Basionie/DSP-Guitar-MultiFX/Mechanical/DSP_3D_Design/Geekcreit 1.3 Inch 4Pin.step.SLDPRT

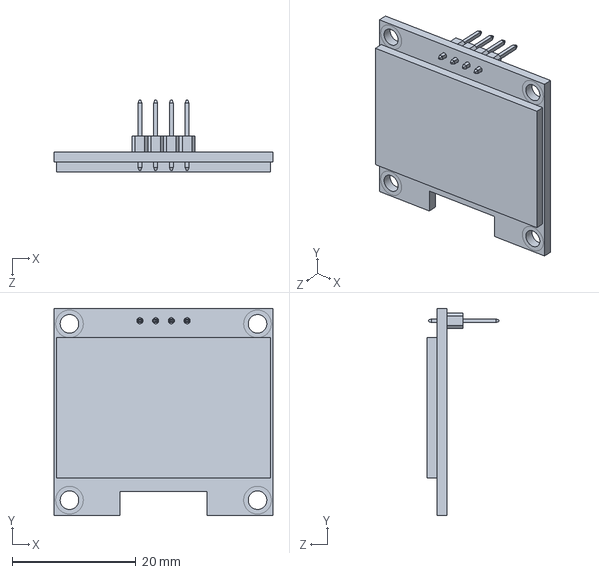
[picture p17: CAD file, 2026-07-20]
Mechanical/DSP_3D_Design/Geekcreit 1.3 Inch 4Pin.step.SLDPRT
35.4 x 33.5 x 11.6 mm
