Basionie/DSP-Guitar-MultiFX/Mechanical/DSP_3D_Design/mts102.SLDASM

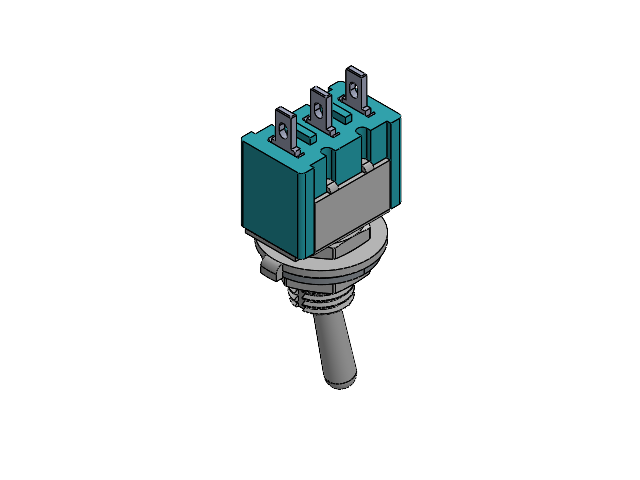
[picture p21: CAD file, 2026-07-20]
Mechanical/DSP_3D_Design/mts102.SLDASM
Metal_part.step
Polyamide_body.step
Terminal.step x 3
Nut_h.step
Internal_Tooth_Lock_Washers.step
Keyed_washer.step
Nut_B.step
