Basionie/DSP-Guitar-MultiFX/Mechanical/DSP_3D_Design/Assem1.SLDASM

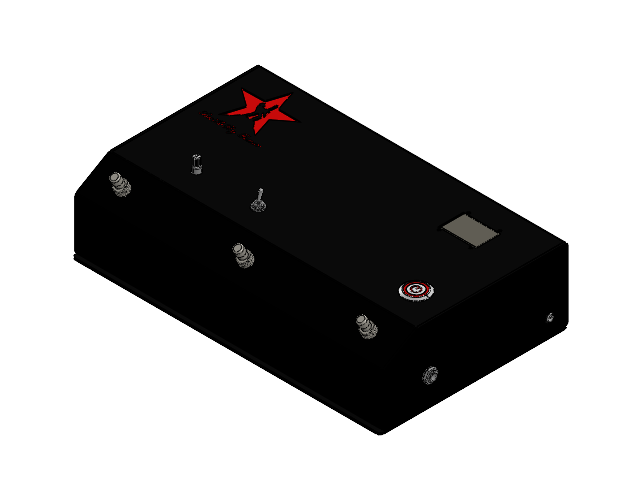
[picture p22: CAD file, 2026-07-20]
Mechanical/DSP_3D_Design/Assem1.SLDASM
Geekcreit 1.3 Inch 4Pin.step
Momentary footswitch x 3
EC11 Rotary Encoder Dode Switch-15mm
Metal Push button Switch with ring LED 22mm
Terminal_1.step x 6
Metal_part_1.step
Polyamid_body.step
Handle.step
Nut_H_1.step
Internal_Tooth_Lock_Washers_1.step
Keyed_wafer.step
Nut_B_1.step
Washer005.step x 2
Sleeve001.step x 2
Common_contact001.step x 2
Washer003.step x 2
Output_contact001.step x 2
Washer004.step x 2
Wacher005.step x 2
Thread001.step x 2
Body009.step x 2
Body023.step x 2
Washer006.step x 2
Female DC-Power-to-Screw-Terminals-Adapter
